wileycousins/lamp/firmware/src/pindefs.h

// lamp
// Copyright 2014 by Wiley Cousins, LLC.
// shared under the terms of the MIT License
//
// file: pindefs.h
// description: pin definitions for the lamp

#ifndef LAMP_PINDEFS_H
#define LAMP_PINDEFS_H

// led stacks
#define NUM_STACKS  3

// unused pins
#define PORTB_UNUSED_MASK  ( (1<<2) | (1<<0) )
#define PORTC_UNUSED_MASK  ( (1<<5) | (1<<1) | (1<<0) )
#define PORTD_UNUSED_MASK  ( (1<<7) | (1<<6) | (1<<5) )

#endif
